koga73/space-clock/src/clock.py

import time
import json
import _thread

from lib.daylightsaving import StandardTimePolicy, DaylightSavingPolicy, DaylightSaving 

_SINGLETON_ENFORCER = object()

# Clock with microsecond precision, timezones and daylight saving time
class Clock:
    ERROR_NOT_SET = "time not set"

    DEFAULT_FORMAT_24HR = False
    DEFAULT_TZ = -5	# EST
    DEFAULT_DST = "us"

    _instance = None

    @staticmethod
    def get_instance():
        if (Clock._instance is None):
            Clock._instance = Clock(_SINGLETON_ENFORCER)
        return Clock._instance

    def __init__(self, enforcer = None):
        if (enforcer != _SINGLETON_ENFORCER):
            raise RuntimeError("Cannot create instance, use singleton instead")

        self._lock = _thread.allocate_lock()

        # Locale settings
        self.format_24hr = Clock.DEFAULT_FORMAT_24HR
        self.tz = Clock.DEFAULT_TZ
        self.dst = Clock.DEFAULT_DST
        
        # Timekeeping in microseconds
        self._time_us = 0
        self._pps_last_tick = 0
        self._pps_ticks_per_second = 1000000

        # Daylight saving time policy
        self._ds = None
    
    # region LOCALE
    def set_locale(self, format_24hr = None, tz = None, dst = None):
        with self._lock:
            if (format_24hr != None):
                self.format_24hr = format_24hr
            if (tz != None):
                self.tz = tz
            if (dst != None):
                self.dst = dst
            
            print("set_locale", json.dumps({
                "format_24hr": format_24hr,
                "tz": tz,
                "dst": dst
            }))
            tz_minutes = self.tz * 60

            # US
            if (self.dst == "us"):
                # Daylight Saving starts on second Sunday of March at 2am
                # 0 = Northern hemisphere
                # 2 = Second week of the month
                # 3 = March
                # 6 = Sunday
                # 2 = 2AM
                # Time offset = 60 mins (GMT+1)
                dst_policy = DaylightSavingPolicy(0, 2, 3, 6, 2, tz_minutes + 60)

                # Daylight Saving ends on first Sunday of November at 2AM
                # 0 = Northern hemisphere
                # 1 = First week of the month
                # 11 = November
                # 6 = Sunday
                # 2 = 2AM
                # Time offset = 0 mins (GMT/UTC)
                std_policy = StandardTimePolicy(0, 1, 11, 6, 2, tz_minutes)

                self._ds = DaylightSaving(dst_policy, std_policy)

            # UK / EU   
            elif (self.dst == "uk"):
                # Daylight Saving starts on last Sunday of March at 1AM
                # 0 = Northern hemisphere
                # 0 = Last week of the month
                # 3 = March
                # 6 = Sunday
                # 1 = 1AM
                # Time offset = 60 mins (GMT+1)
                dst_policy = DaylightSavingPolicy(0, 0, 3, 6, 1, tz_minutes + 60)

                # Daylight Saving ends on last Sunday of October at 2AM
                # 0 = Northern hemisphere
                # 0 = Last week of the month
                # 10 = October
                # 6 = Sunday
                # 2 = 2AM
                # Time offset = 0 mins (GMT/UTC)
                std_policy = StandardTimePolicy(0, 0, 10, 6, 2, tz_minutes)

                self._ds = DaylightSaving(dst_policy, std_policy)
            
            # Australia
            elif (self.dst == "au"):
                # Daylight Saving starts on first Sunday of October at 2am
                # 1 = Southern hemisphere
                # 1 = First week of the month
                # 10 = October
                # 6 = Sunday
                # 2 = 2AM
                # Time offset = 60 mins (GMT+1)
                dst_policy = DaylightSavingPolicy(1, 1, 10, 6, 2, tz_minutes + 60)

                # Daylight Saving ends on first Sunday of April at 3AM
                # 1 = Southern hemisphere
                # 1 = First week of the month
                # 4 = April
                # 6 = Sunday
                # 3 = 3AM
                # Time offset = 0 mins (GMT/UTC)
                std_policy = StandardTimePolicy(1, 1, 4, 6, 3, tz_minutes)

                self._ds = DaylightSaving(dst_policy, std_policy)
            
            else:
                self._ds = None
    
    def get_locale(self):
        with self._lock:
            return (self.format_24hr, self.tz, self.dst)

    # dt = (year, month, day, weekday, hours, minutes, seconds, subseconds)
    def get_localtime(self):
        try:
            seconds, microseconds = self.get_seconds()
        except ValueError:
            return (1970, 1, 1, 4, 0, 0, 0, 0)
        
        with self._lock:
            ds = self._ds
            tz = self.tz

        if (ds != None):
            # Adjust seconds for timezone and daylight saving time
            seconds = ds.localtime(seconds)
        else:
            # Adjust seconds for timezone only
            seconds += tz * 60 * 60
        
        # Convert seconds back to datetime tuple with microsecond precision
        year, month, mday, hour, minute, second, weekday, yearday = time.gmtime(seconds)
        return (year, month, mday, weekday, hour, minute, second, microseconds)

    def get_timestamp_local(self):
        dt = self.get_localtime()
        return self._format_timestamp(dt[0], dt[1], dt[2], dt[4], dt[5], dt[6], dt[7])
    # endregion
    
    # region DATETIME
    # SET datetime UTC where subseconds = microseconds
    # dt = (year, month, day, weekday, hours, minutes, seconds, subseconds)
    # pps = (last_pps_tick, ticks_per_second)
    def set_datetime(self, dt, pps):
        # Convert datetime tuple to seconds since epoch (UNIX: January 1, 1970)
        seconds = time.mktime((dt[0], dt[1], dt[2], dt[4], dt[5], dt[6], dt[3], 0))

        pps_last_tick, pps_ticks_per_second = pps
        
        # Assume the subseconds in tuple is in Microseconds
        nema_us = (seconds * 1000000) + dt[7]
        tick_gap = time.ticks_diff(time.ticks_us(), pps_last_tick)
        gap_us = (tick_gap * 1000000) // pps_ticks_per_second

        with self._lock:
            self._time_us = nema_us - gap_us
            self._pps_last_tick = pps_last_tick
            self._pps_ticks_per_second = pps_ticks_per_second

    # GET datetime UTC tuple where subseconds = microseconds
    # dt = (year, month, day, weekday, hours, minutes, seconds, subseconds)
    def get_datetime(self):
        try:
            seconds, microseconds = self.get_seconds()
        except ValueError:
            return (1970, 1, 1, 4, 0, 0, 0, 0)

        year, month, mday, hour, minute, second, weekday, yearday = time.gmtime(seconds)
        return (year, month, mday, weekday, hour, minute, second, microseconds)

    def get_timestamp(self):
        dt = self.get_datetime()
        return self._format_timestamp(dt[0], dt[1], dt[2], dt[4], dt[5], dt[6], dt[7])
    # endregion

    # GET time in seconds since epoch (UNIX: January 1, 1970)
    def get_seconds(self):
        with self._lock:
            t = self._time_us
            pps_last_tick = self._pps_last_tick
            pps_ticks_per_second = self._pps_ticks_per_second

        if (t == 0):
            raise ValueError(Clock.ERROR_NOT_SET)

        delta = time.ticks_diff(time.ticks_us(), pps_last_tick)
        now = t + (delta * 1000000) // pps_ticks_per_second
        return int(now // 1000000), int(now % 1000000)
    
    # What to show on the display
    def get_display(self, digits = 4):
        with self._lock:
            is_unset = self._time_us == 0
            is_24hr = self.format_24hr
        
        if (is_unset):
            return "------" if digits == 6 else "----"

        now = self.get_localtime()
        hours = now[4]
        minutes = now[5]
        seconds = now[6]

        if (not is_24hr):
            hours = hours % 12
            if (hours == 0):
                hours = 12

        hours_str = "{:2d}".format(hours)
        minutes_str = "{:02d}".format(minutes)
        seconds_str = "{:02d}".format(seconds)
        
        return f'{hours_str}{minutes_str}{seconds_str}' if digits == 6 else f'{hours_str}{minutes_str}'
    # endregion

    def _format_timestamp(self, year, month, day, hours, minutes, seconds, microseconds):
        # Pad with leading zero if needed
        year = "{:02d}".format(year)
        month = "{:02d}".format(month)
        day = "{:02d}".format(day)
        hours = "{:02d}".format(hours)
        minutes = "{:02d}".format(minutes)
        seconds = "{:02d}".format(seconds)
        microseconds = "{:06d}".format(microseconds)

        return f"{year}-{month}-{day} {hours}:{minutes}:{seconds}.{microseconds}"
